princeloki11/hc-soundbox/schematics/HC_SoundBox.kicad_sch

## KiCad design schematics/HC_SoundBox.kicad_sch (2026-05-03)

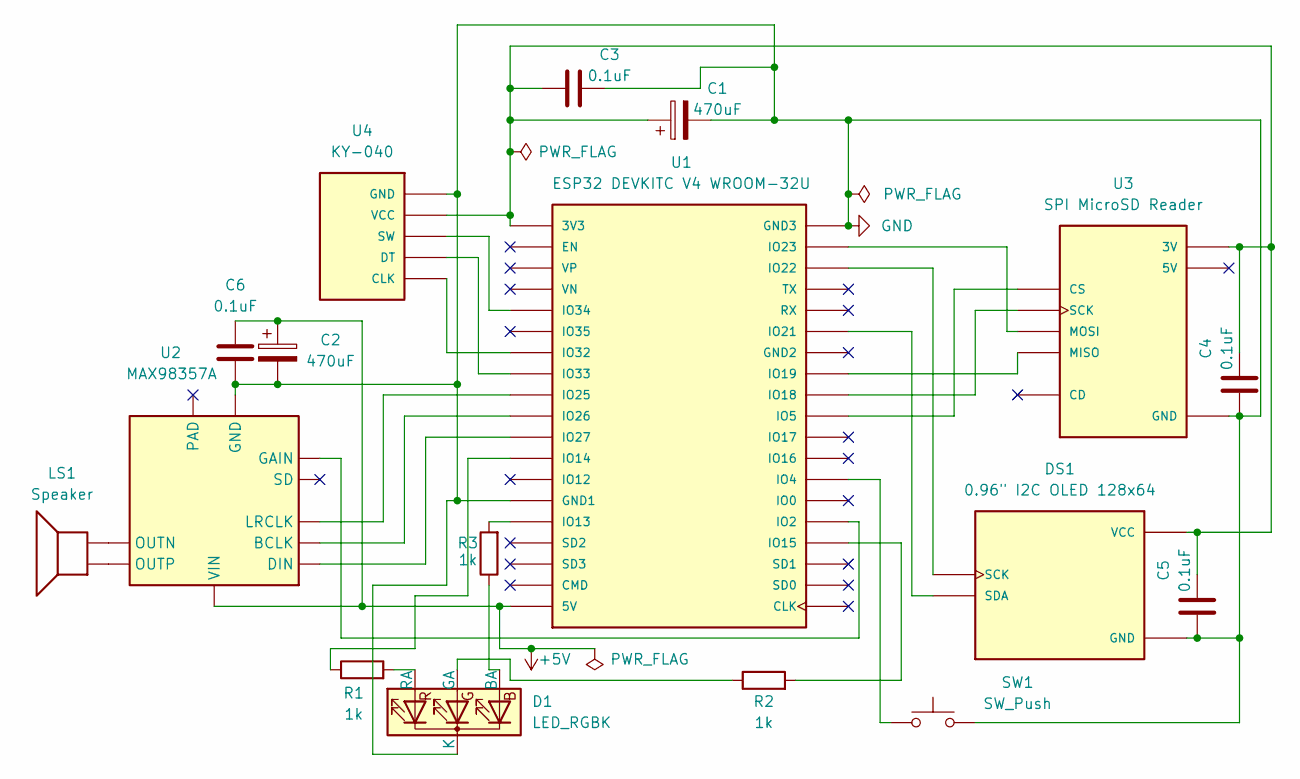
[picture p2: schematic HC_SoundBox.kicad_sch]

Parts:
C1, C2: 470uF
C3, C4, C5, C6: 0.1uF
D1: LED_RGBK
DS1: 0.96" I2C OLED 128x64; LCD_OLED_128X64_1.3_I2C; PARTREV NA
LS1: Speaker
R1, R2, R3: 1k
SW1: SW_Push
U1: ESP32 DEVKITC V4 WROOM-32U; MODULE_ESP32-DEVKITC-32U; PARTREV V4
U2: MAX98357A; TQFN-16-1EP_3x3mm_P0.5mm_EP1.23x1.23mm
U3: SPI MicroSD Reader; MODULE_254; PARTREV Jul 31, 2013
U4: KY-040; KY-040-PORT

Connections:
+5V: C2.1, C6.1, U1.19 (5V), U2.7 (VIN), U2.8 (VDD)
GND: C1.2, C2.2, C3.1, C4.2, C5.2, C6.2, D1.4 (K), DS1.2 (GND), SW1.2, U1.14 (GND1), U1.38 (GND3), U2.3 (GND), U2.11 (GND), U2.15 (GND), U3.6 (GND), U4.GND
unnamed: C1.1, C3.2, C4.1, C5.1, DS1.1 (VCC), U1.1 (3V3), U3.7 (3V), U4.VCC
unnamed: D1.1 (RA), R1.2
unnamed: D1.2 (GA), R2.1
unnamed: D1.3 (BA), R3.1
unnamed: DS1.3 (SCK), U1.36 (IO22)
unnamed: DS1.4 (SDA), U1.33 (IO21)
unnamed: LS1.1, U2.9 (OUTP)
unnamed: LS1.2, U2.10 (OUTN)
unnamed: R1.1, U1.12 (IO14)
unnamed: R2.2, U1.23 (IO15)
unnamed: R3.2, U1.15 (IO13)
unnamed: SW1.1, U1.26 (IO4)
unnamed: U1.5 (IO34), U4.SW
unnamed: U1.7 (IO32), U4.CLK
unnamed: U1.8 (IO33), U4.DT
unnamed: U1.9 (IO25), U2.14 (LRCLK)
unnamed: U1.10 (IO26), U2.16 (BCLK)
unnamed: U1.11 (IO27), U2.1 (DIN)
unnamed: U1.24 (IO2), U2.2 (GAIN)
unnamed: U1.29 (IO5), U3.2 (CS)
unnamed: U1.30 (IO18), U3.5 (SCK)
unnamed: U1.31 (IO19), U3.4 (MISO)
unnamed: U1.37 (IO23), U3.3 (MOSI)
