princeloki11/hc-soundbox/src/rgb/rgb.h

#pragma once
#include <Arduino.h>

void initRgb();
void setRgbWhite();
void setRgbRed();
void setRgbGreen();
void setRgbPurple();
void setRgbBlue();
void setRgbRainbow(bool enabled);
void updateRgb();
